maxthorson/goober/hardware/mockups/gerber-bottom.png

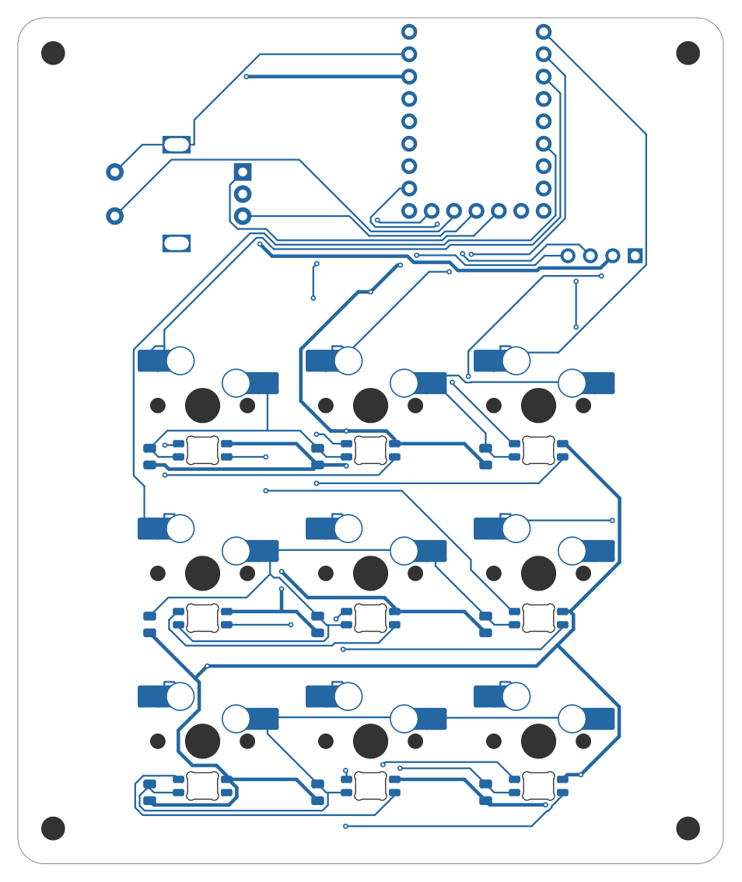
hardware/mockups/gerber-bottom.png
