maxthorson/goober/hardware/mockups/gerber-top.png

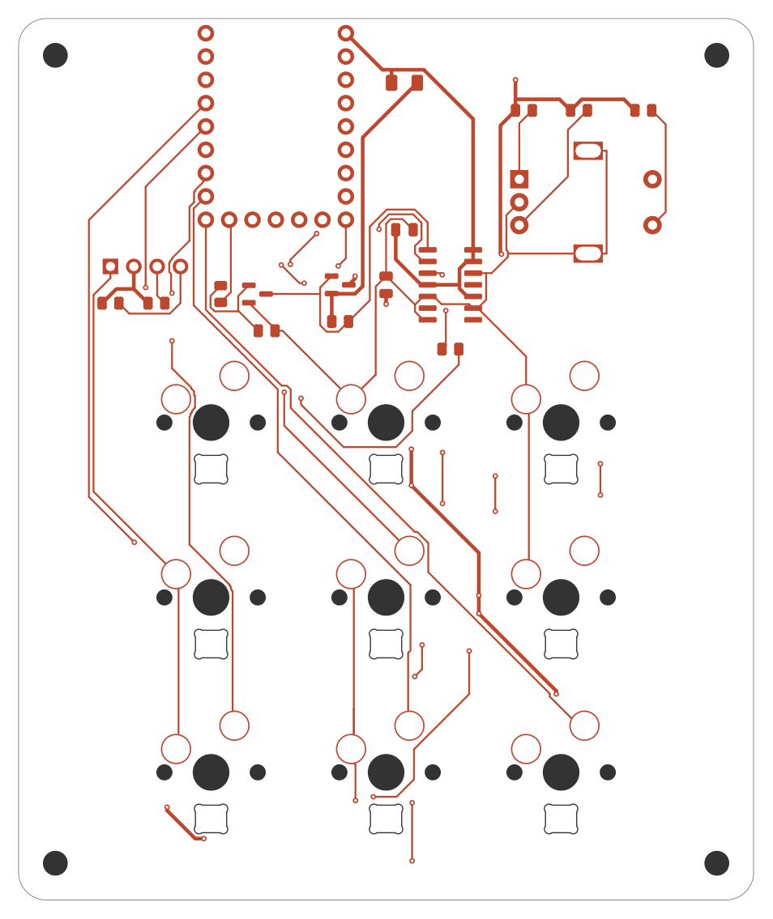
hardware/mockups/gerber-top.png
