maxthorson/goober/hardware/mockups/goober-appearance.png

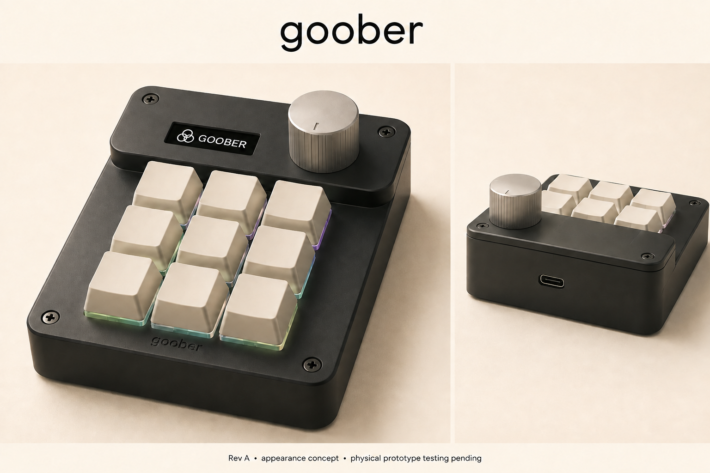
hardware/mockups/goober-appearance.png
