maxthorson/goober/hardware/mockups/pcb-top.png

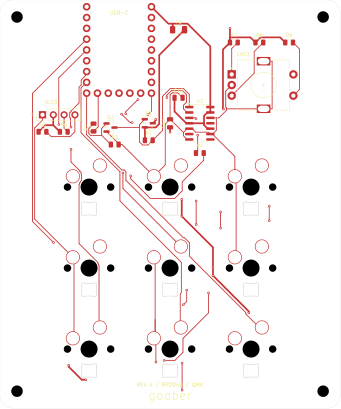
hardware/mockups/pcb-top.png
