maxthorson/goober/hardware/validation/schematic/goober.png

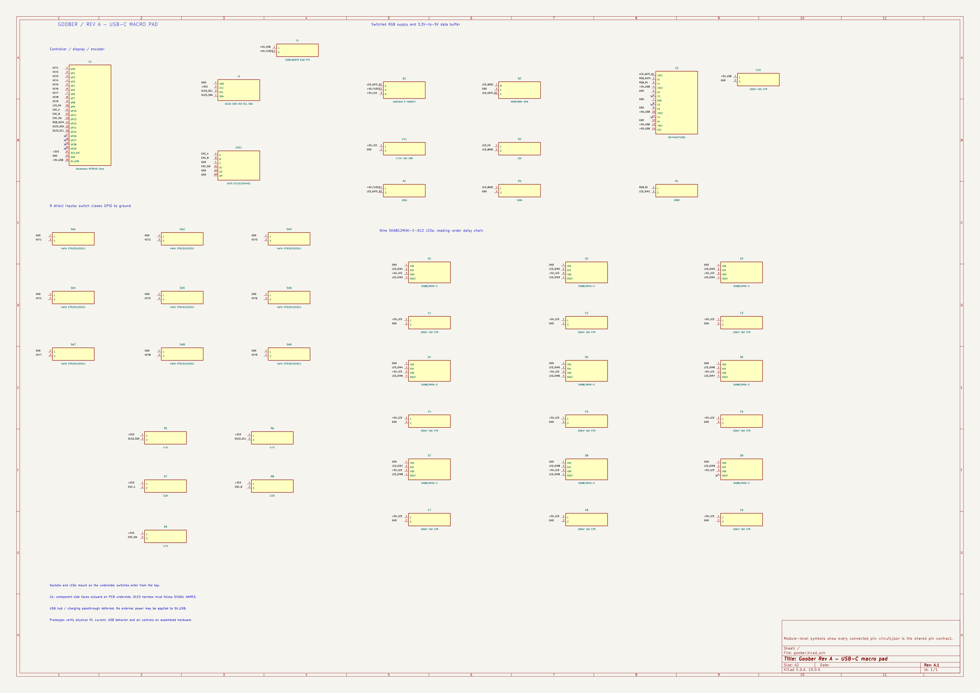
hardware/validation/schematic/goober.png
